INTO-CPS-Association/plant-controller/STATUS.md

# Project Status

## 23-September-2026

Plant Controller updated with version 3.
Version 3 expands differs from version 1 in these ways

* Submersible pumps are 12V DC motors instead
* AutomationHAT has been replaced with MODBUS RTU connected CS-IO404 relay
* A MODBUS RTU bus line is added for extensibility with professional sensor units
* Soil sensors are replaced with DF Robot Moisture, temperature, EC soil sensors

## 01-March-2025

Plant Controller - 1 and plants are on display in the hallway.

## Plant Controller - 1

This case study has

* Three large plants
* One Raspberry Pi 5
* SHT45 (temperature and humidity) and AS7341 (light) sensors
* Three 15V submersible DC motors
* AutomationHAT
* One 12V DC power supply
* Three stands to properly place watering pipes in the plants

## Plant Controller - 2 (Under Construction)

This case study has

* Two medium size basil plants
* One Raspberry Pi 3
* senseHAT
* Waveshare relay HAT
* Two 5V submersible DC motors
* Three stands to properly place watering pipes in the plants
