INTO-CPS-Association/plant-controller/docs/pt/controller_1/parts/hardware-pictures/AS7341-adafruit.jpg

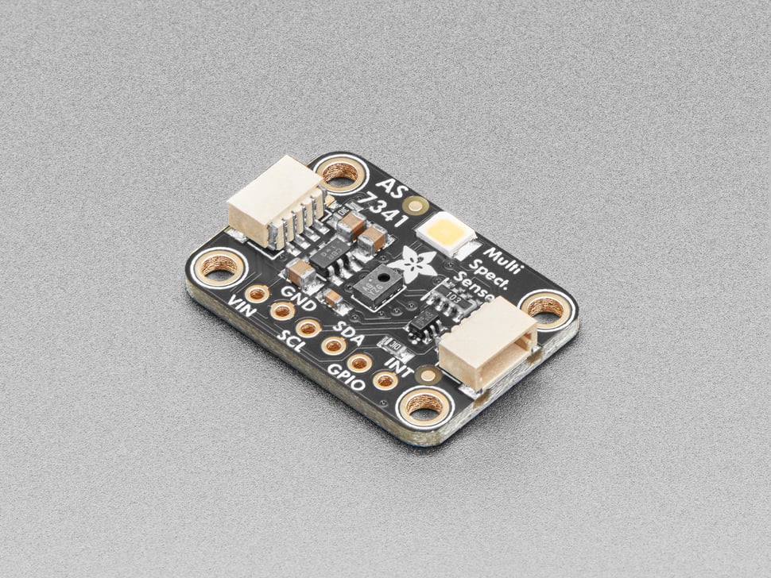
docs/pt/controller_1/parts/hardware-pictures/AS7341-adafruit.jpg
