INTO-CPS-Association/plant-controller/docs/pt/controller_1/PT-schematic-physical-v0.1.1-1.png

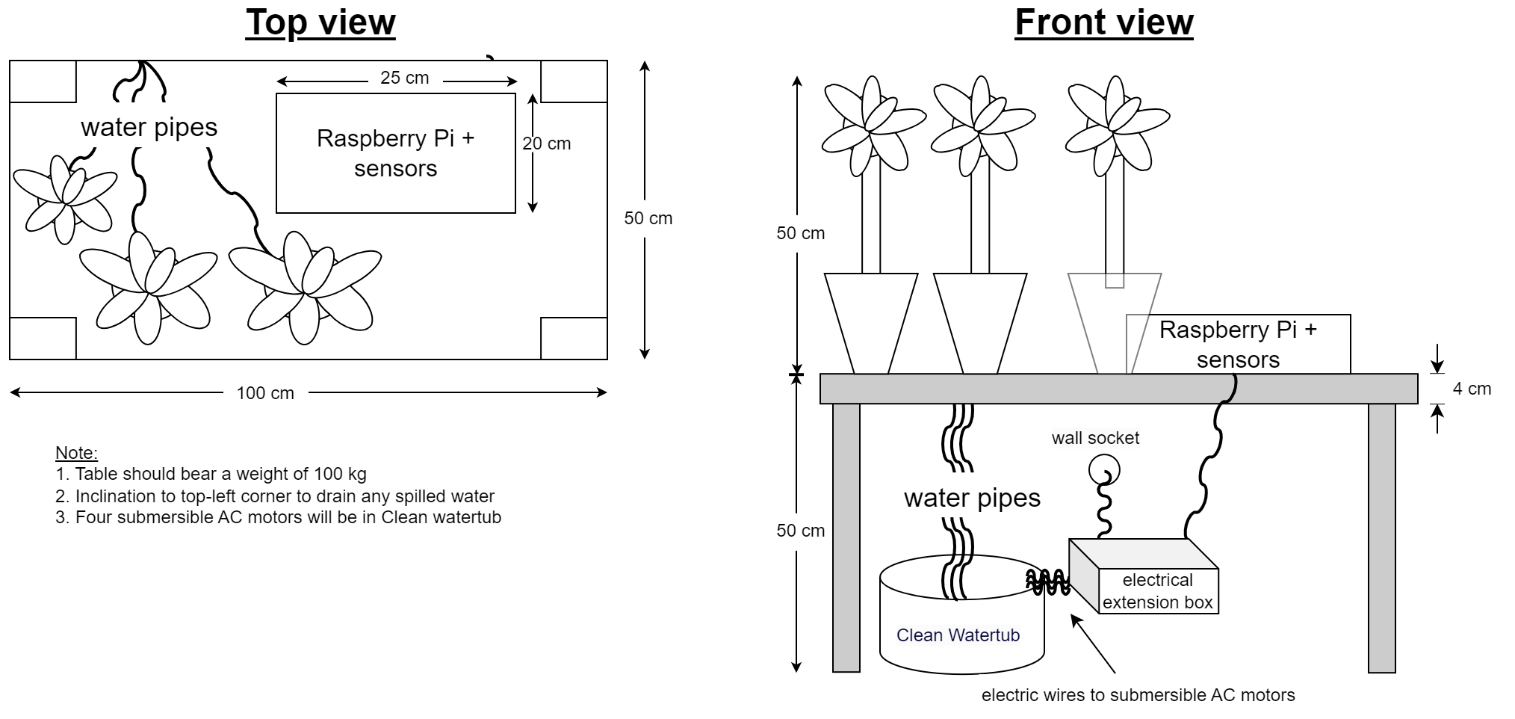
docs/pt/controller_1/PT-schematic-physical-v0.1.1-1.png
