INTO-CPS-Association/plant-controller/docs/pt/controller_3/documentation/hardware/diagrams/greenhouse_sensor_plus_multiplexer_connections.png

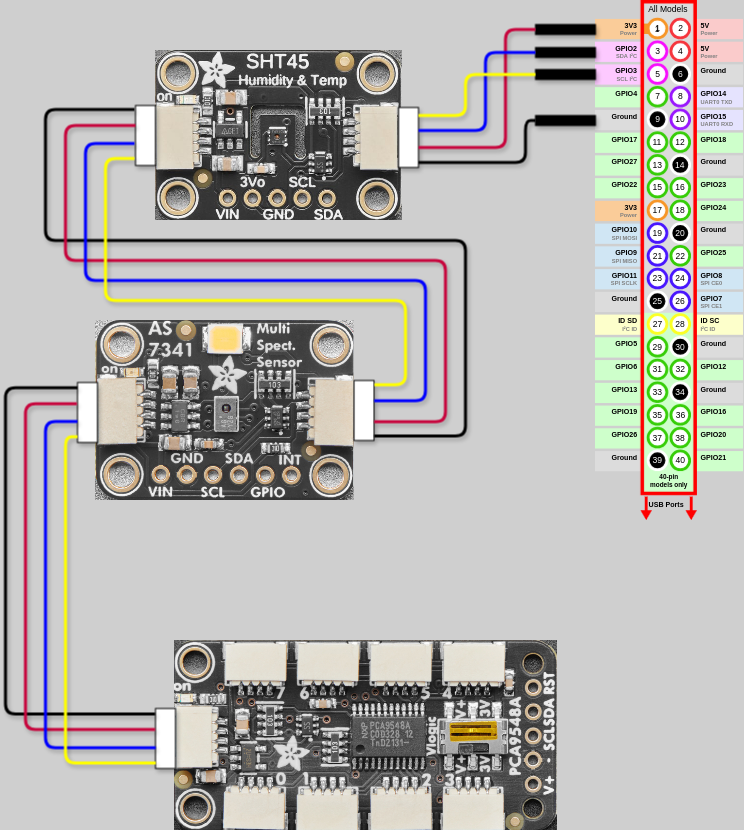
docs/pt/controller_3/documentation/hardware/diagrams/greenhouse_sensor_plus_multiplexer_connections.png
