INTO-CPS-Association/plant-controller/docs/pt/controller_3/documentation/hardware/components/lever_connector_top_down.png

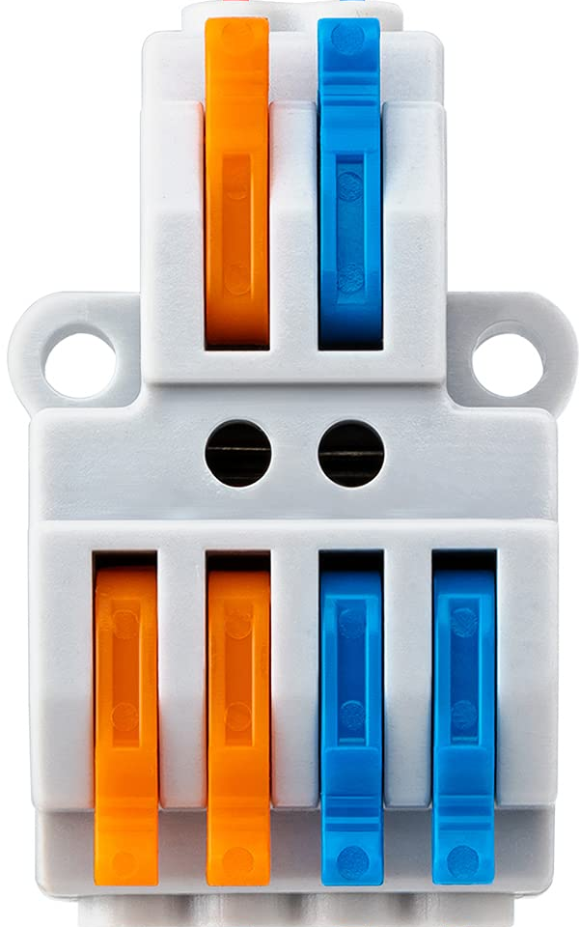
docs/pt/controller_3/documentation/hardware/components/lever_connector_top_down.png
