INTO-CPS-Association/plant-controller/docs/pt/controller_3/documentation/hardware/components/pca9548_topdown.jpg

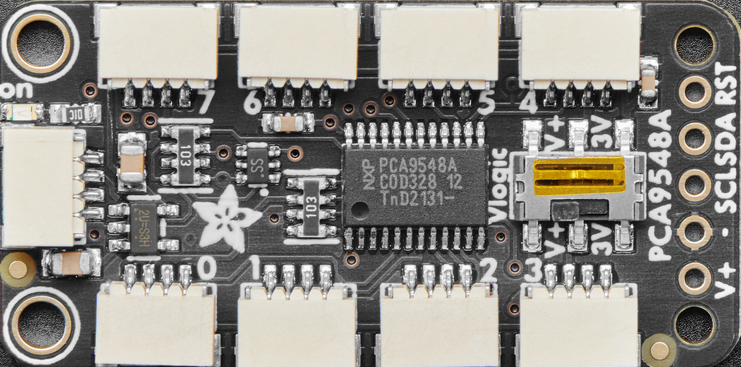
docs/pt/controller_3/documentation/hardware/components/pca9548_topdown.jpg
