INTO-CPS-Association/plant-controller/docs/pt/controller_3/documentation/hardware/components/PI_5_TOP.png

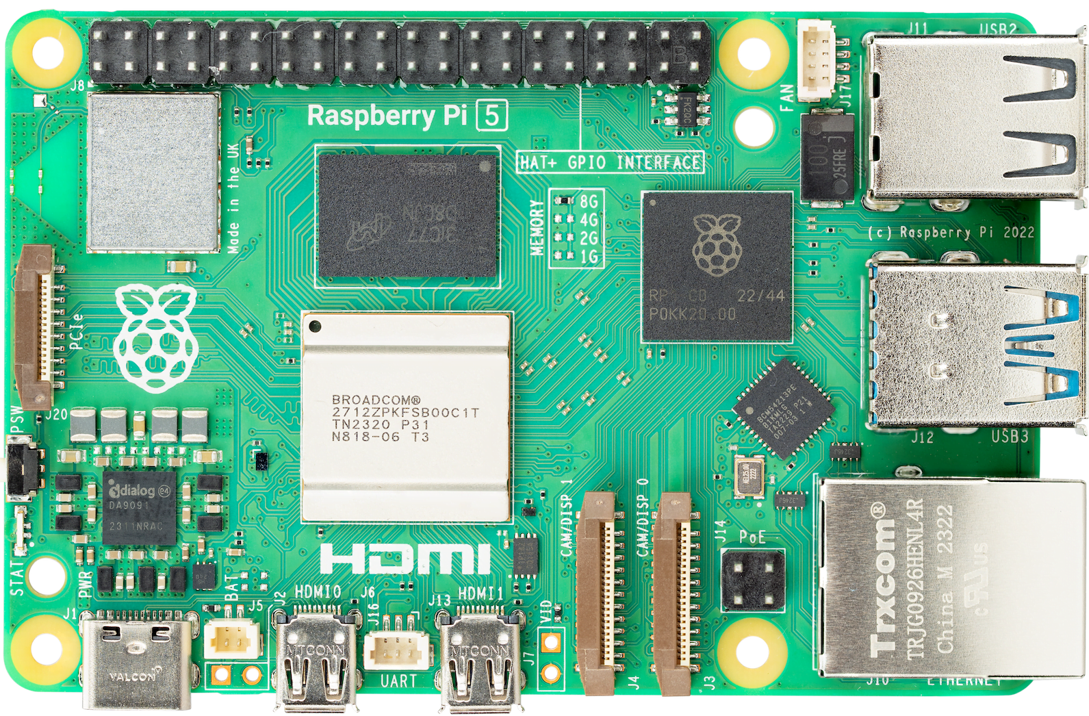
docs/pt/controller_3/documentation/hardware/components/PI_5_TOP.png
