INTO-CPS-Association/plant-controller/docs/pt/controller_3/documentation/hardware/components/pump_closeup.jpeg

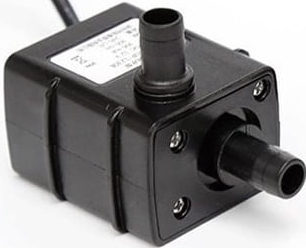
docs/pt/controller_3/documentation/hardware/components/pump_closeup.jpeg
