INTO-CPS-Association/plant-controller/docs/pt/controller_3/documentation/hardware/components/sub_to_rs485_top_down_sans_usb.png

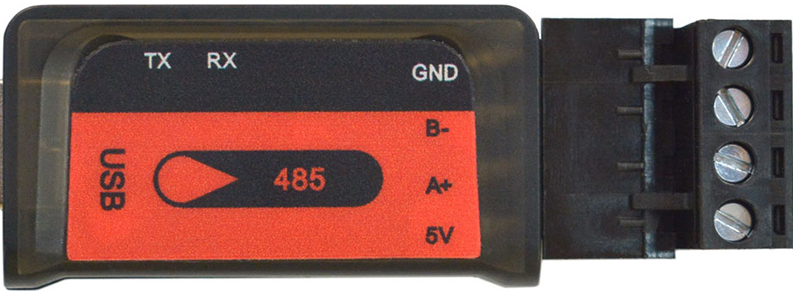
docs/pt/controller_3/documentation/hardware/components/sub_to_rs485_top_down_sans_usb.png
