INTO-CPS-Association/plant-controller/docs/pt/controller_3/documentation/hardware/components/top_down.png

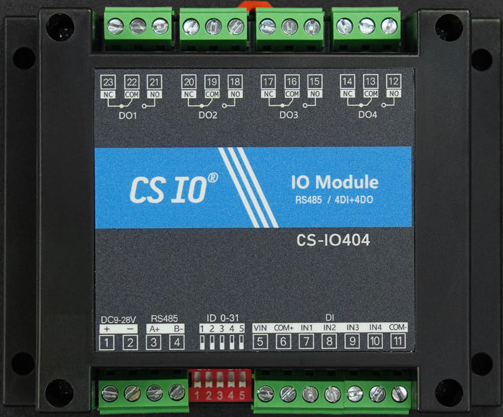
docs/pt/controller_3/documentation/hardware/components/top_down.png
