INTO-CPS-Association/plant-controller/docs/pt/controller_1/installation-1/installation-1.jpg

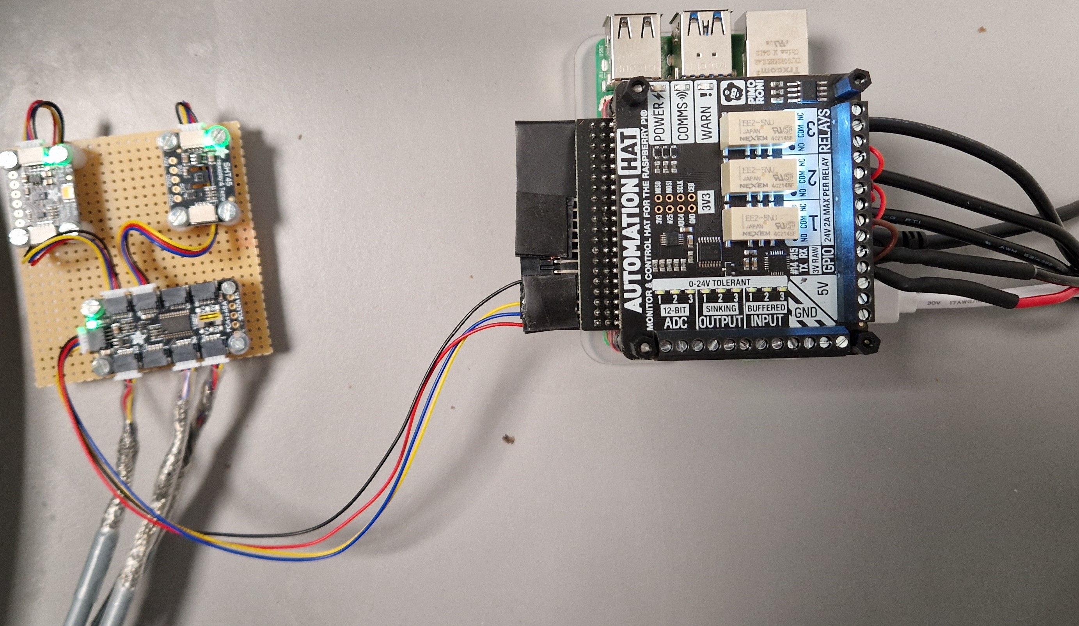
docs/pt/controller_1/installation-1/installation-1.jpg
