INTO-CPS-Association/plant-controller/docs/pt/controller_1/installation-1/installation-1_with-cover-top-view.jpg

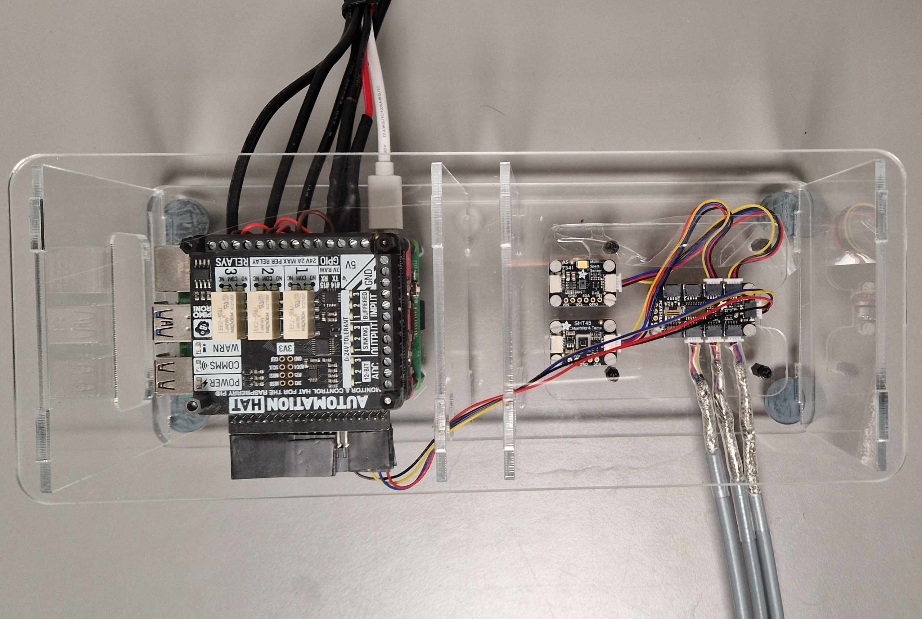
docs/pt/controller_1/installation-1/installation-1_with-cover-top-view.jpg
